jerwil/Count_Up_Time/Photos/IMG_2620.JPG

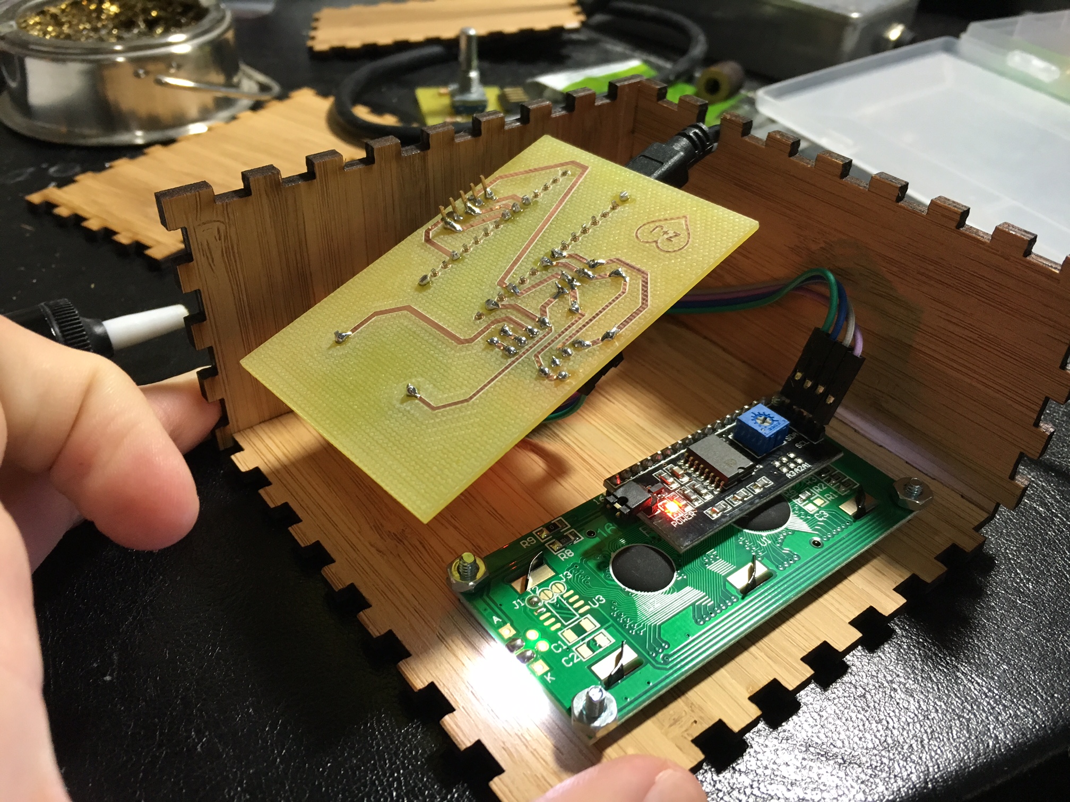
Photos/IMG_2620.JPG
